hallard/Lora-Breakout/Lora-Breakout-bot.png

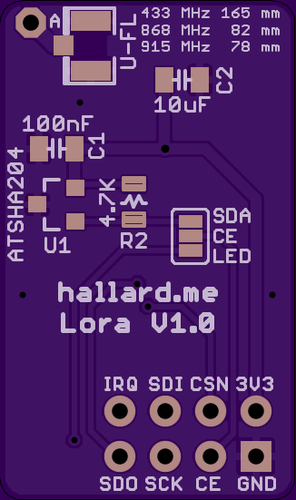
Lora-Breakout-bot.png
