hallard/Lora-Breakout/Lora-Breakout-sch.png

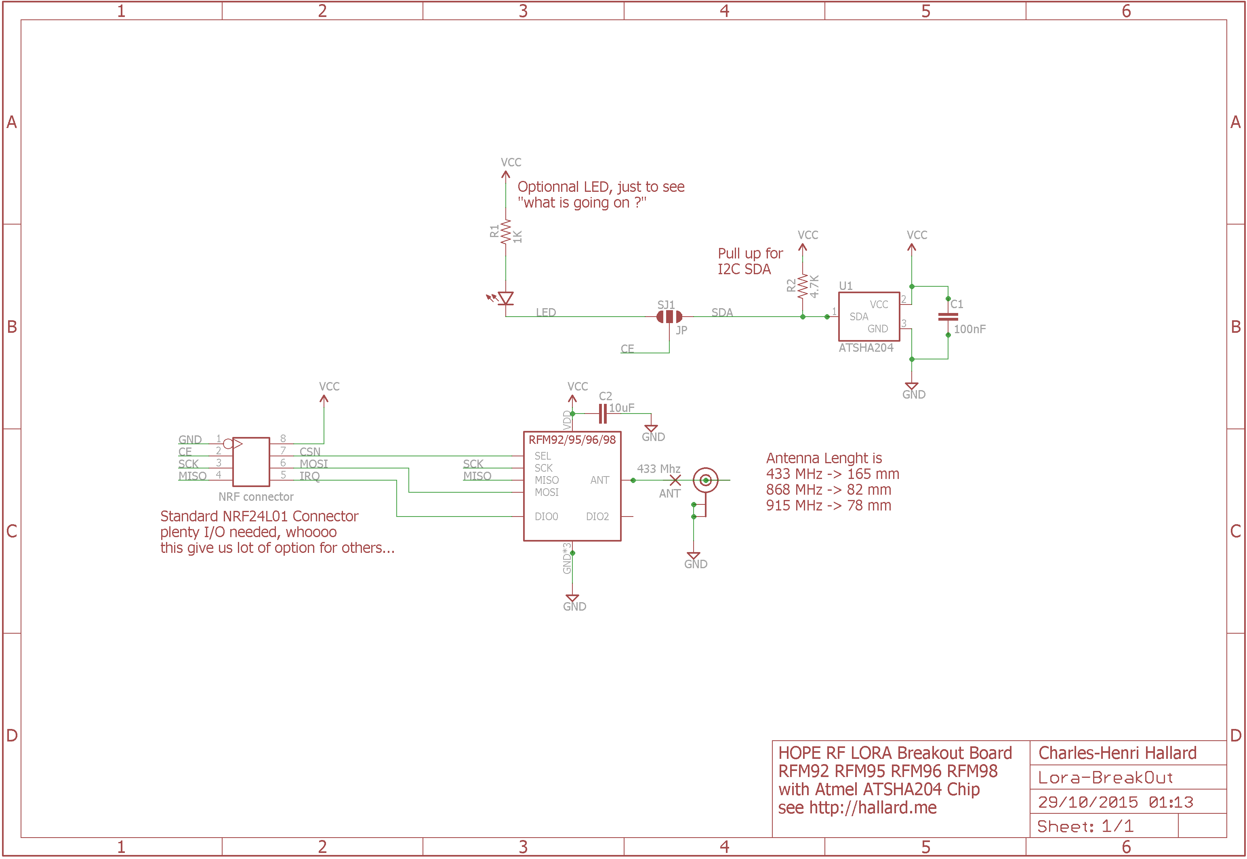
Lora-Breakout-sch.png
